anabdck/automatic-equalizer/Calculo dos Filtros/Figuras/Equacoes MFB_PB 3.png

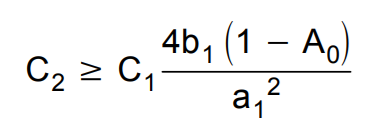
Calculo dos Filtros/Figuras/Equacoes MFB_PB 3.png
