anabdck/automatic-equalizer/Calculo dos Filtros/Figuras/Tabela Bessel.png

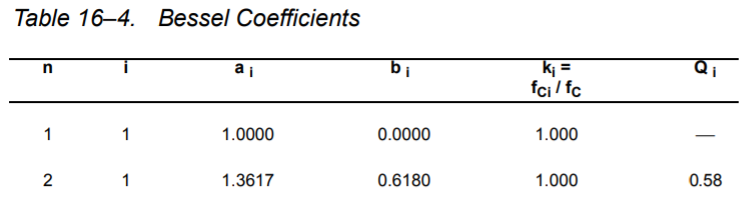
Calculo dos Filtros/Figuras/Tabela Bessel.png
