anabdck/automatic-equalizer/Calculo dos Filtros/Figuras/tabela MFB_PB.png

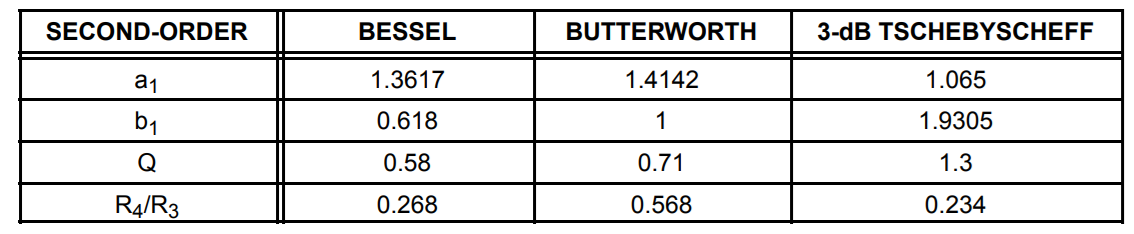
Calculo dos Filtros/Figuras/tabela MFB_PB.png
