anabdck/automatic-equalizer/Resultados - Circuito VCA/Análise do Ganho e Fase em Função da Tensão de Controle/Dados Adquiridos em Bancada/VCA_ganho_-1000m.csv

5 | 202.0000E-3 | 7.4400 | -1000.0000E-3 | 1.3826
10 | 198.0000E-3 | 7.5200 | -1000.0000E-3 | 1.0360
15 | 198.0000E-3 | 7.4400 | -1000.0000E-3 | 517.2414E-3
20 | 202.0000E-3 | 7.4400 | -1.0000 | 1.3793
30 | 202.0000E-3 | 7.4400 | -1.0000 | 0.0E+0
40 | 200.0000E-3 | 7.4400 | -1.0000 | -970.3504E-3
50 | 200.0000E-3 | 7.4400 | -1.0000 | -518.9813E-3
60 | 198.0000E-3 | 7.4400 | -1.0000 | 414.7465E-3
70 | 200.0000E-3 | 7.4400 | -1.0000 | 241.9355E-3
80 | 200.0000E-3 | 7.4400 | -1.0000 | 1.3783
90 | 200.0000E-3 | 7.4400 | -1.0000 | 1.2414
100 | 200.0000E-3 | 7.4400 | -1.0000 | -692.3077E-3
200 | 198.0000E-3 | 7.4400 | -1000.0000E-3 | -553.8462E-3
300 | 200.0000E-3 | 7.4400 | -1000.0000E-3 | 1.0369
400 | 200.0000E-3 | 7.4400 | -1000.0000E-3 | 832.0493E-3
500 | 202.0000E-3 | 7.4400 | -1000.0000E-3 | 346.1538E-3
600 | 202.0000E-3 | 7.4400 | -1000.0000E-3 | 826.6361E-3
700 | 200.0000E-3 | 7.4400 | -1000.0000E-3 | 726.7833E-3
800 | 200.0000E-3 | 7.4400 | -1000.0000E-3 | 138.3551E-3
900 | 202.0000E-3 | 7.4400 | -1000.0000E-3 | 1.5517
1000 | 202.0000E-3 | 7.4400 | -1000.0000E-3 | 1.3820
1500 | 202.0000E-3 | 7.4400 | -1.0000 | 1.6657
2000 | 202.0000E-3 | 7.4400 | -1.0000 | 1.9325
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
