anabdck/automatic-equalizer/Resultados - Circuito VCA/Análise do Ganho e Fase em Função da Tensão de Controle/Dados Adquiridos em Bancada/VCA_ganho_-1500m.csv

5 | 200.0000E-3 | 6.5600 | -1.5201 | 1.0365
10 | 200.0000E-3 | 6.6400 | -1.5200 | -520.9841E-3
15 | 200.0000E-3 | 6.6400 | -1.5200 | 173.0769E-3
20 | 198.0000E-3 | 6.6400 | -1.5201 | -276.7102E-3
30 | 202.0000E-3 | 6.6400 | -1.5201 | -415.2249E-3
40 | 198.0000E-3 | 6.6400 | -1.5200 | -554.4859E-3
50 | 198.0000E-3 | 6.6400 | -1.5200 | 344.8276E-3
60 | 198.0000E-3 | 6.6400 | -1.5200 | 0.0E+0
70 | 200.0000E-3 | 6.6400 | -1.5203 | 1.2863
80 | 202.0000E-3 | 6.6400 | -1.5201 | 552.1472E-3
90 | 200.0000E-3 | 6.6400 | -1.5202 | 311.4187E-3
100 | 198.0000E-3 | 6.6400 | -1.5201 | 692.3077E-3
200 | 200.0000E-3 | 6.6400 | -1.5201 | 827.5862E-3
300 | 202.0000E-3 | 6.6400 | -1.5200 | 830.4498E-3
400 | 200.0000E-3 | 6.6400 | -1.5200 | -276.9231E-3
500 | 200.0000E-3 | 6.6400 | -1.5200 | 1.7308
600 | 202.0000E-3 | 6.6400 | -1.5201 | 207.2539E-3
700 | 202.0000E-3 | 6.6400 | -1.5201 | 121.5395E-3
800 | 202.0000E-3 | 6.6400 | -1.5200 | 1.1047
900 | 202.0000E-3 | 6.6400 | -1.5206 | 1.2414
1000 | 202.0000E-3 | 6.6400 | -1.5201 | 1.9002
1500 | 202.0000E-3 | 6.6400 | -1.5201 | 1.1396
2000 | 202.0000E-3 | 6.6400 | -1.5200 | 693.1074E-3
2500 | 202.0000E-3 | 6.6400 | -1.5202 | 1.3900
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
