anabdck/automatic-equalizer/Resultados - Circuito VCA/Análise do Ganho e Fase em Função da Tensão de Controle/Dados Adquiridos em Bancada/VCA_ganho_-2000m.csv

5 | 198.0000E-3 | 5.8800 | -2.0000 | -692.3077E-3
10 | 202.0000E-3 | 5.8800 | -2.0000 | -689.6552E-3
15 | 198.0000E-3 | 5.9200 | -2.0000 | -517.9856E-3
20 | 200.0000E-3 | 5.9200 | -2.0000 | 138.3020E-3
30 | 200.0000E-3 | 5.9200 | -2.0000 | 935.3349E-3
40 | 200.0000E-3 | 5.9200 | -1.9999 | 2.2086
50 | 200.0000E-3 | 5.9200 | -2.0000 | 690.9789E-3
60 | 202.0000E-3 | 5.9200 | -2.0000 | 1.6552
70 | 200.0000E-3 | 5.9200 | -2.0000 | -969.0444E-3
80 | 200.0000E-3 | 5.9200 | -2.0000 | 415.2249E-3
90 | 200.0000E-3 | 5.9200 | -2.0000 | 0.0E+0
100 | 200.0000E-3 | 5.9200 | -2.0000 | 345.6553E-3
200 | 200.0000E-3 | 5.9200 | -2.0000 | 1.2442
300 | 202.0000E-3 | 5.9200 | -2.0000 | 1.4541
400 | 200.0000E-3 | 5.9200 | -2.0000 | 1.6615
500 | 200.0000E-3 | 5.9200 | -2.0000 | 1.2057
600 | 200.0000E-3 | 5.8800 | -2.0000 | 414.2693E-3
700 | 202.0000E-3 | 5.8800 | -2.0000 | 1.2081
800 | 200.0000E-3 | 5.8800 | -2.0000 | 3.0275
900 | 202.0000E-3 | 5.8800 | -2.0000 | 1.5517
1000 | 202.0000E-3 | 5.8800 | -2.0000 | 0.0E+0
1500 | 202.0000E-3 | 5.8400 | -2.0000 | 1.2442
2000 | 202.0000E-3 | 5.8400 | -2.0000 | 1.3846
2500 | 202.0000E-3 | 5.8800 | -2.0000 | 0.0E+0
3000 | 202.0000E-3 | 5.8800 | -2.0000 | 2.4828
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
