anabdck/automatic-equalizer/Resultados - Circuito VCA/Análise do Ganho e Fase em Função da Tensão de Controle/Dados Adquiridos em Bancada/VCA_ganho_-2500m.csv

5 | 198.0000E-3 | 5.0400 | -2.5081 | 1.3820
10 | 200.0000E-3 | 5.0400 | -2.5104 | -1.7341
15 | 200.0000E-3 | 5.0400 | -2.5069 | 0.0E+0
20 | 198.0000E-3 | 5.0400 | -2.5064 | 1.1060
30 | 198.0000E-3 | 5.0400 | -2.5058 | -207.3733E-3
40 | 200.0000E-3 | 5.0800 | -2.5057 | -1.1094
50 | 200.0000E-3 | 5.0800 | -2.5037 | 1.7274
60 | 198.0000E-3 | 5.0800 | -2.5108 | 415.0653E-3
70 | 198.0000E-3 | 5.0800 | -2.5096 | 483.8710E-3
80 | 202.0000E-3 | 5.0400 | -2.5100 | 276.3916E-3
90 | 198.0000E-3 | 5.0400 | -2.5094 | 309.9440E-3
100 | 200.0000E-3 | 5.0400 | -2.5110 | -691.6427E-3
200 | 198.0000E-3 | 5.0400 | -2.5113 | 827.9034E-3
300 | 200.0000E-3 | 5.0400 | -2.5122 | -623.5566E-3
400 | 202.0000E-3 | 5.0400 | -2.5100 | -832.6908E-3
500 | 202.0000E-3 | 5.0400 | -2.5133 | 0.0E+0
600 | 200.0000E-3 | 5.0400 | -2.5099 | 414.7465E-3
700 | 200.0000E-3 | 5.0400 | -2.5143 | 1.2064
800 | 202.0000E-3 | 5.0400 | -2.5125 | 2.2120
900 | 202.0000E-3 | 5.0400 | -2.5083 | -730.9645E-3
1000 | 200.0000E-3 | 5.0400 | -2.5060 | -346.4870E-3
1500 | 202.0000E-3 | 5.0400 | -2.5116 | 1.1376
2000 | 202.0000E-3 | 5.0400 | -2.5146 | 1.3767
2500 | 202.0000E-3 | 5.0000 | -2.5003 | 1.7241
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
