anabdck/automatic-equalizer/Simulações/Filtro_PB.asc

C1: cap; 100n
C2: cap; 200n
R1: res; 200k
R2: res; 100k
R3: res; 100k
R4: res; 180k
R5: res; 12k
U1: TL072_TI
V1: voltage; -15
V2: voltage; 15
V3: voltage; SINE(0 15 100); AC 1 0
Named nets: 0, Vdd, Vee, Vin
.ac dec 100 1 10000
