anabdck/automatic-equalizer/Simulações/Project_V2.asc

C1: cap; 150nF
C2: cap; 150nF
C3: cap; 56nF
C4: cap; 56nF
C5: cap; 20nF
C6: cap; 20nF
C7: cap; 15nF
C8: cap; 15nF
C9: cap; 5.6nF
C10: cap; 5.6nF
C11: cap; 150nF
C12: cap; 47nF
C13: cap; 2.7nF
C14: cap; 10nF
C15: cap; 10nF
C16: cap; 10nF
C17: cap; 10nF
C18: cap; 10nF
C19: cap; 10nF
C20: cap; 10nF
C21: cap; 10nF
J1: njf; BF245C
J2: njf; BF245C
J3: njf; BF245C
J4: njf; BF245C
J5: njf; BF245C
J6: njf; BF245C
J7: njf; BF245C
J8: njf; BF245C
R1: res; 100k
R2: res; 12k
R3: res; 10k
R4: res; 68k
R5: res; 8k2
R6: res; 6k8
R7: res; 47k
R8: res; 5k6
R9: res; 4k7
R10: res; 15k
R11: res; 2k
R12: res; 1k5
R13: res; 10K
R14: res; 1k2
R15: res; 1k
R16: res; 47k
R17: res; 200k
R18: res; 10k
R19: res; 10k
R20: res; 10k
R21: res; 10k
R22: res; 10k
R23: res; 10k
R24: res; 10k
R25: res; 10k
R26: res; 10k
R27: res; 10k
R28: res; 10k
R29: res; 10k
R30: res; 10k
R31: res; 10k
R32: res; 68
R33: res; 100k
R34: res; 100k
R35: res; 100k
R36: res; 100k
R37: res; 100k
R38: res; 100k
R39: res; 100k
R40: res; 1Meg
R41: res; 100k
R42: res; 1Meg
R43: res; 1Meg
R44: res; 1Meg
R45: res; 5k6
R46: res; 30k
R47: res; 1Meg
R48: res; 1Meg
R49: res; 5k6
R50: res; 30k
R51: res; 1Meg
R52: res; 1Meg
R53: res; 5k6
R54: res; 30k
R55: res; 1Meg
R56: res; 1Meg
R57: res; 5k6
R58: res; 30k
R59: res; 1Meg
R60: res; 1Meg
R61: res; 5k6
R62: res; 30k
R63: res; 1Meg
R64: res; 1Meg
R65: res; 5k6
R66: res; 30k
R67: res; 1Meg
R68: res; 1Meg
R69: res; 5k6
R70: res; 30k
R71: res; 5k6
U1: TL072_TI
U2: TL072_TI
U3: TL072_TI
U4: TL072_TI
U5: TL072_TI
U6: TL072_TI
U7: TL072_TI
U8: spdt
U9: TL072_TI
U10: spdt
U11: TL072_TI
U12: spdt
U13: TL072_TI
U14: spdt
U15: TL072_TI
U16: spdt
U17: TL072_TI
U18: spdt
U19: TL072_TI
U20: spdt
U21: TL072_TI
U22: TL072_TI
U23: TL072_TI
U24: TL072_TI
U25: TL072_TI
U26: TL072_TI
U27: TL072_TI
U28: TL072_TI
U29: TL072_TI
V1: voltage; -15
V2: voltage; 15
V3: voltage; SINE(0 1 100); AC 1 0
V4: voltage; -5
V5: voltage; -5
V6: voltage; -5
V7: voltage; -5
V8: voltage; -5
V9: voltage; -5
V10: voltage; -5
V11: voltage; -5
Named nets: 0, Vdd, Vee, Vout_1_1, Vin, Vout_2_1, Vout_3_1, Vout_4_1, Vout_5_1, Vout_1_2, Vout_2_2, Vout_3_2, Vout_4_2, Vout_5_2, Vout_6_1, Vout_6_2, Vout_7_1, Vout_7_2, Vout_1_3, Vout_2_3, Vout_3_3, Vout_4_3, Vout_5_3, Vout_6_3, Vout_7_3, Vctrl_1, Vctrl_2, Vctrl_3, Vctrl_4, Vctrl_5, Vctrl_6, Vctrl_7, Vctrl, Vout
.ac dec 100 50 20k
