anabdck/automatic-equalizer/Simulações/VCA circuit v2.asc

C1: cap; 10nF
J1: njf; BF245C
Q1: npn; BC547B
R1: res; 1Meg
R2: res; 1Meg
R3: res; 5k6
R4: res; 30k
R5: res; 1Meg
U1: opamp2; LM324
V1: voltage; 0
V2: voltage; SINE(0 .1 20k)
V3: voltage; 15V
V4: voltage; 15V
Named nets: 0, 15V, -15V
.tran 0 .0002 0 .001
.inc opamp.lib
