anabdck/automatic-equalizer/Simulações/VCA circuit.asc

C1: cap; 10nF
J1: njf; BF245C
R1: res; 1Meg
R2: res; 1Meg
R3: res; 5k6
R4: res; 30k
U1: opamp2; LM324
V1: voltage; -3
V2: voltage; SINE(0 .1 20k)
V3: voltage; 15V
V4: voltage; 15V
Named nets: 0, 15V, -15V
.tran 0 .0002 0 .001
.inc opamp.lib
